MaxMax-embedded/jkbms_hardware_reverse_engineering/images/jk_backside.jpg

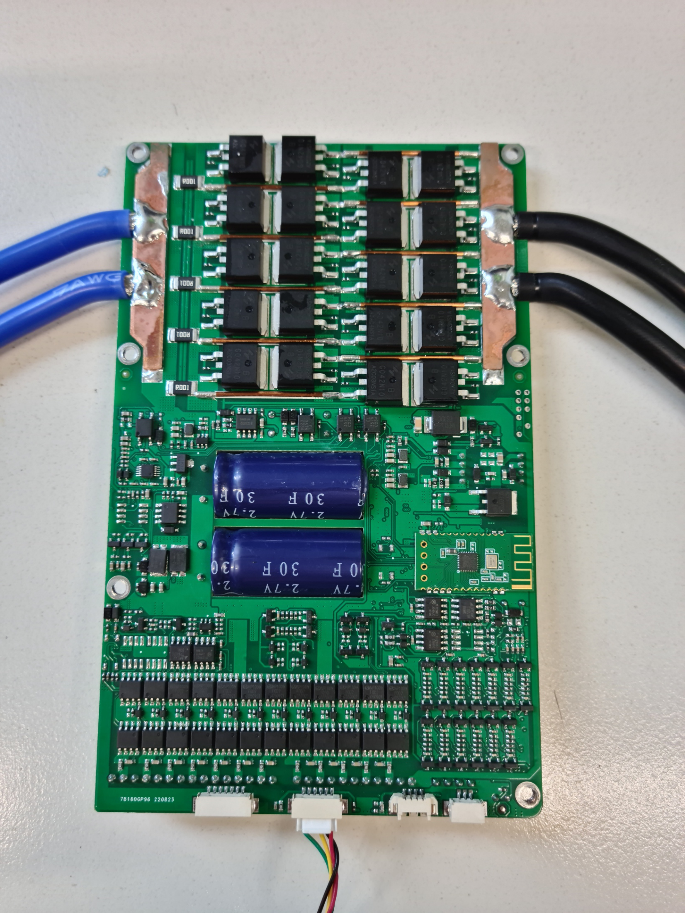
images/jk_backside.jpg
