MaxMax-embedded/jkbms_hardware_reverse_engineering/circuits/balancing_circuitry/balancing_circuitry.kicad_pcb

## KiCad design schematics/Microbee_Kit_Core_Board/Microbee_Kit_Core_Board.kicad_sch

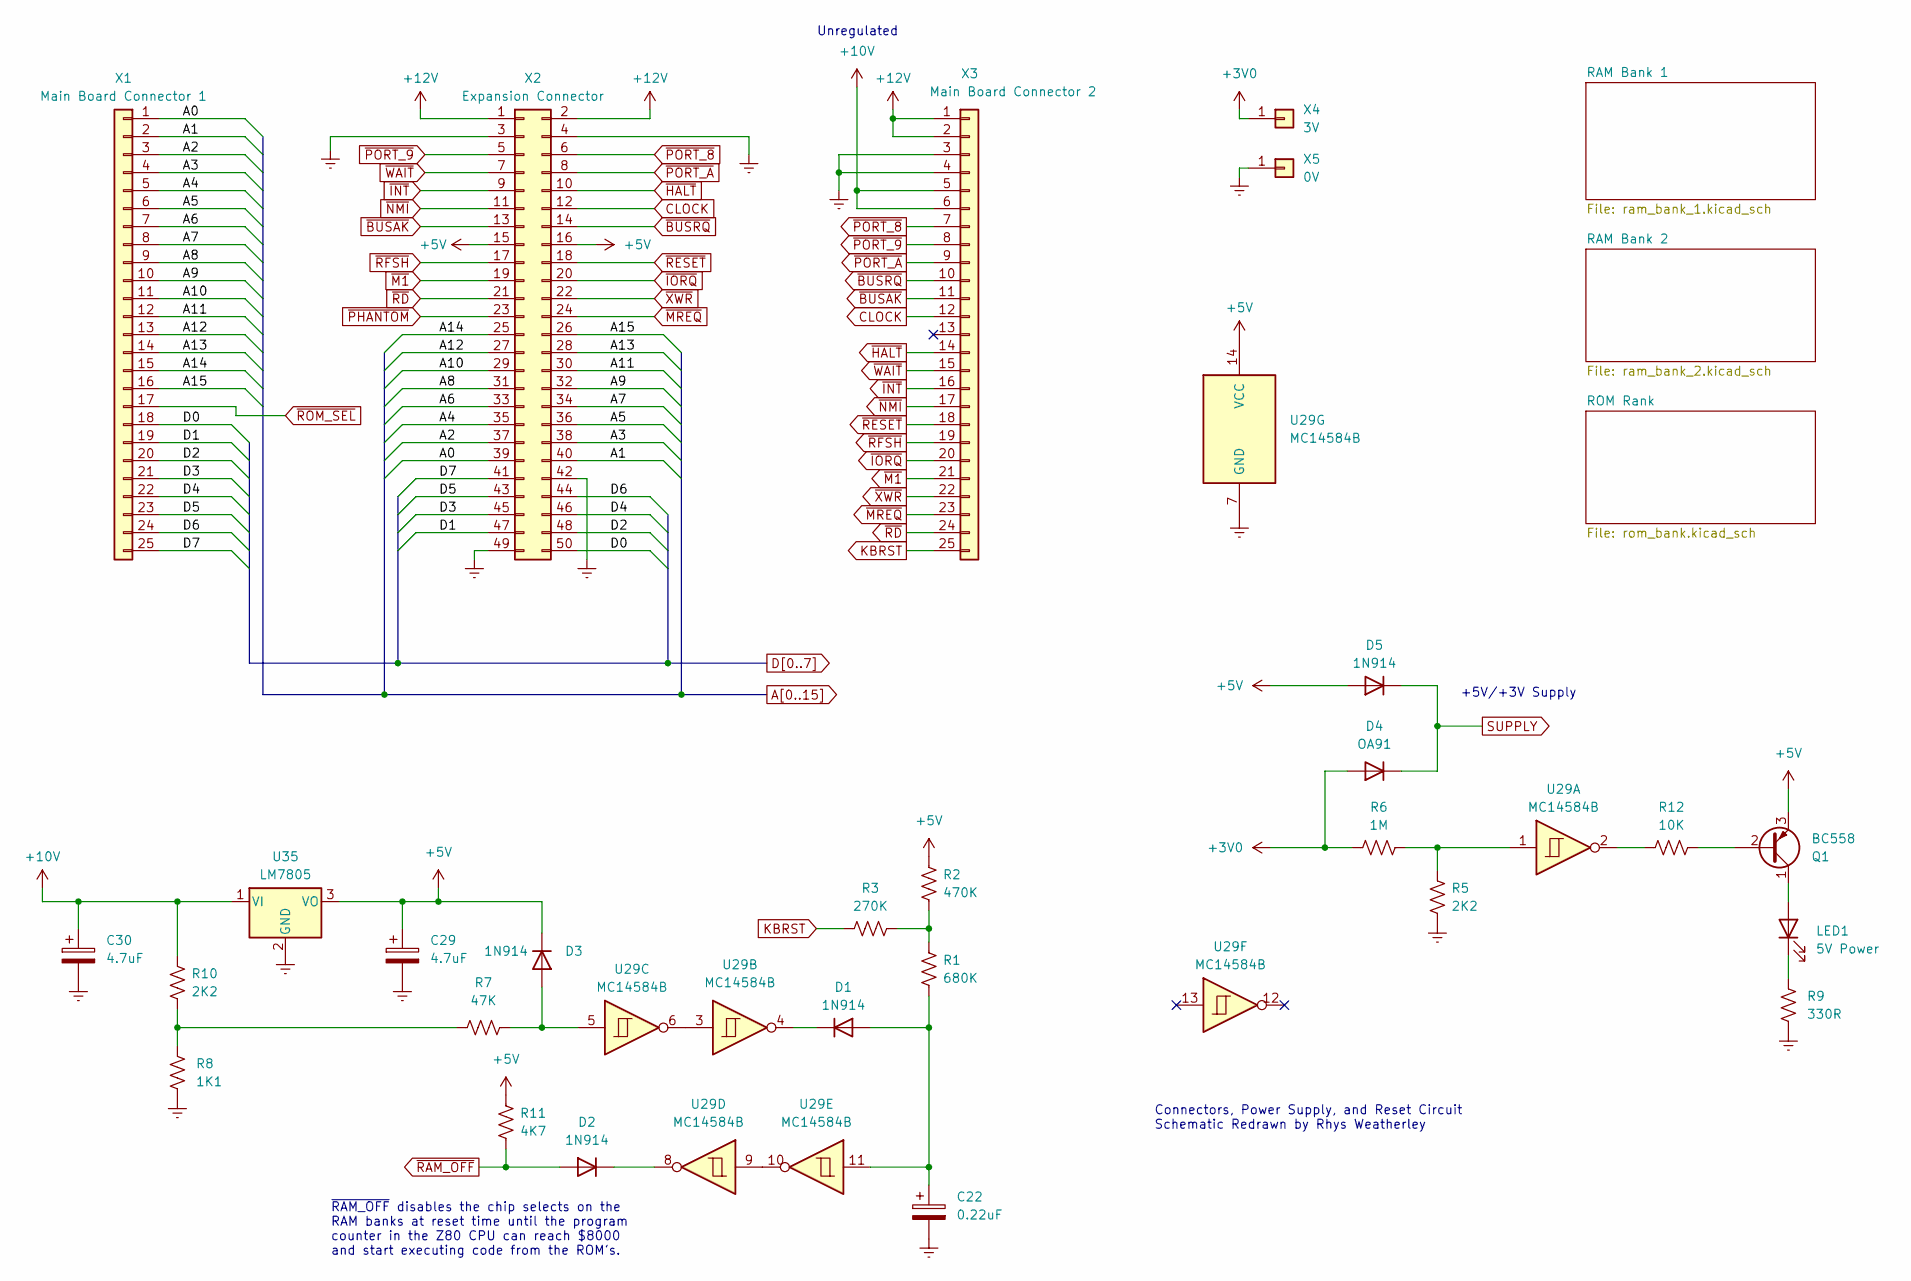
[picture p6: schematic Microbee_Kit_Core_Board.kicad_sch]

Parts:
C22: 0.22uF
C29, C30: 4.7uF
D1, D2, D3, D5: 1N914; D_DO-35_SOD27_P10.16mm_Horizontal
D4: OA91; D_DO-35_SOD27_P10.16mm_Horizontal
LED1: 5V Power
Q1: BC558; TO-92_Inline
R1: 680K; R_Axial_DIN0207_L6.3mm_D2.5mm_P10.16mm_Horizontal
R2: 470K; R_Axial_DIN0207_L6.3mm_D2.5mm_P10.16mm_Horizontal
R3: 270K; R_Axial_DIN0207_L6.3mm_D2.5mm_P10.16mm_Horizontal
R5, R10: 2K2; R_Axial_DIN0207_L6.3mm_D2.5mm_P10.16mm_Horizontal
R6: 1M; R_Axial_DIN0207_L6.3mm_D2.5mm_P10.16mm_Horizontal
R7: 47K; R_Axial_DIN0207_L6.3mm_D2.5mm_P10.16mm_Horizontal
R8: 1K1; R_Axial_DIN0207_L6.3mm_D2.5mm_P10.16mm_Horizontal
R9: 330R; R_Axial_DIN0207_L6.3mm_D2.5mm_P10.16mm_Horizontal
R11: 4K7; R_Axial_DIN0207_L6.3mm_D2.5mm_P10.16mm_Horizontal
R12: 10K; R_Axial_DIN0207_L6.3mm_D2.5mm_P10.16mm_Horizontal
U29: MC14584B; DIP-14_W7.62mm
U35: LM7805; TO-220-3_Vertical
X1: Main Board Connector 1; PinHeader_1x25_P2.54mm_Vertical
X2: Expansion Connector; PinHeader_2x25_P2.54mm_Vertical
X3: Main Board Connector 2; PinHeader_1x25_P2.54mm_Vertical
X4: 3V; PinHeader_1x01_P2.54mm_Vertical
X5: 0V; PinHeader_1x01_P2.54mm_Vertical

Connections:
+3V0: D4.2 (A), R6.1, X4.1
+5V: C29.1, D3.1 (K), D5.2 (A), Q1.3 (E), R2.1, R11.1, U29.14 (VCC), U35.3 (VO), X2.15, X2.16
+10V: C30.1, R10.1, U35.1 (VI), X3.5, X3.6
+12V: X2.1, X2.2, X3.1, X3.2
A0: X1.1, X2.39
A1: X1.2, X2.40
A2: X1.3, X2.37
A3: X1.4, X2.38
A4: X1.5, X2.35
A5: X1.6, X2.36
A6: X1.7, X2.33
A7: X1.8, X2.34
A8: X1.9, X2.31
A9: X1.10, X2.32
A10: X1.11, X2.29
A11: X1.12, X2.30
A12: X1.13, X2.27
A13: X1.14, X2.28
A14: X1.15, X2.25
A15: X1.16, X2.26
CLOCK: X2.12, X3.12
D0: X1.18, X2.50
D1: X1.19, X2.47
D2: X1.20, X2.48
D3: X1.21, X2.45
D4: X1.22, X2.46
D5: X1.23, X2.43
D6: X1.24, X2.44
D7: X1.25, X2.41
Earth: C22.2, C29.2, C30.2, R5.2, R8.2, R9.2, U29.7 (GND), U35.2 (GND), X2.3, X2.4, X2.42, X2.49, X3.3, X3.4, X5.1
KBRST: R3.1, X3.25
unnamed: C22.1, D1.2 (A), R1.2, U29.11
unnamed: D1.1 (K), U29.4
unnamed: D2.1 (K), U29.8
unnamed: D3.2 (A), R7.2, U29.5
unnamed: LED1.1 (K), R9.1
unnamed: LED1.2 (A), Q1.1 (C)
unnamed: Q1.2 (B), R12.2
unnamed: R1.1, R2.2, R3.2
unnamed: R5.1, R6.2, U29.1
unnamed: R7.1, R8.1, R10.2
unnamed: R12.1, U29.2
unnamed: U29.3, U29.6
unnamed: U29.9, U29.10
SUPPLY: D4.1 (K), D5.1 (K)
~BUSAK: X2.13, X3.11
~BUSRQ: X2.14, X3.10
~HALT: X2.10, X3.14
~INT: X2.9, X3.16
~IORQ: X2.20, X3.20
~M1: X2.19, X3.21
~MREQ: X2.24, X3.23
~NMI: X2.11, X3.17
~PHANTOM: X2.23
~PORT_8: X2.6, X3.7
~PORT_9: X2.5, X3.8
~PORT_A: X2.8, X3.9
~RAM_OFF: D2.2 (A), R11.2
~RD: X2.21, X3.24
~RESET: X2.18, X3.18
~RFSH: X2.17, X3.19
~ROM_SEL: X1.17
~WAIT: X2.7, X3.15
~XWR: X2.22, X3.22

Notes on the sheet:
Connectors, Power Supply, and Reset Circuit Schematic Redrawn by Rhys Weatherley
Unregulated
~{RAM_OFF} disables the chip selects on the RAM banks at reset time until the program counter in the Z80 CPU can reach $8000 and start executing code from the ROM's.
+5V/+3V Supply
