MaxMax-embedded/jkbms_hardware_reverse_engineering/circuits/balancing_circuitry/balancing_circuitry.kicad_pcb

## KiCad design schematics/Microbee_Kit_Main_Board/Microbee_Kit_Main_Board.kicad_sch

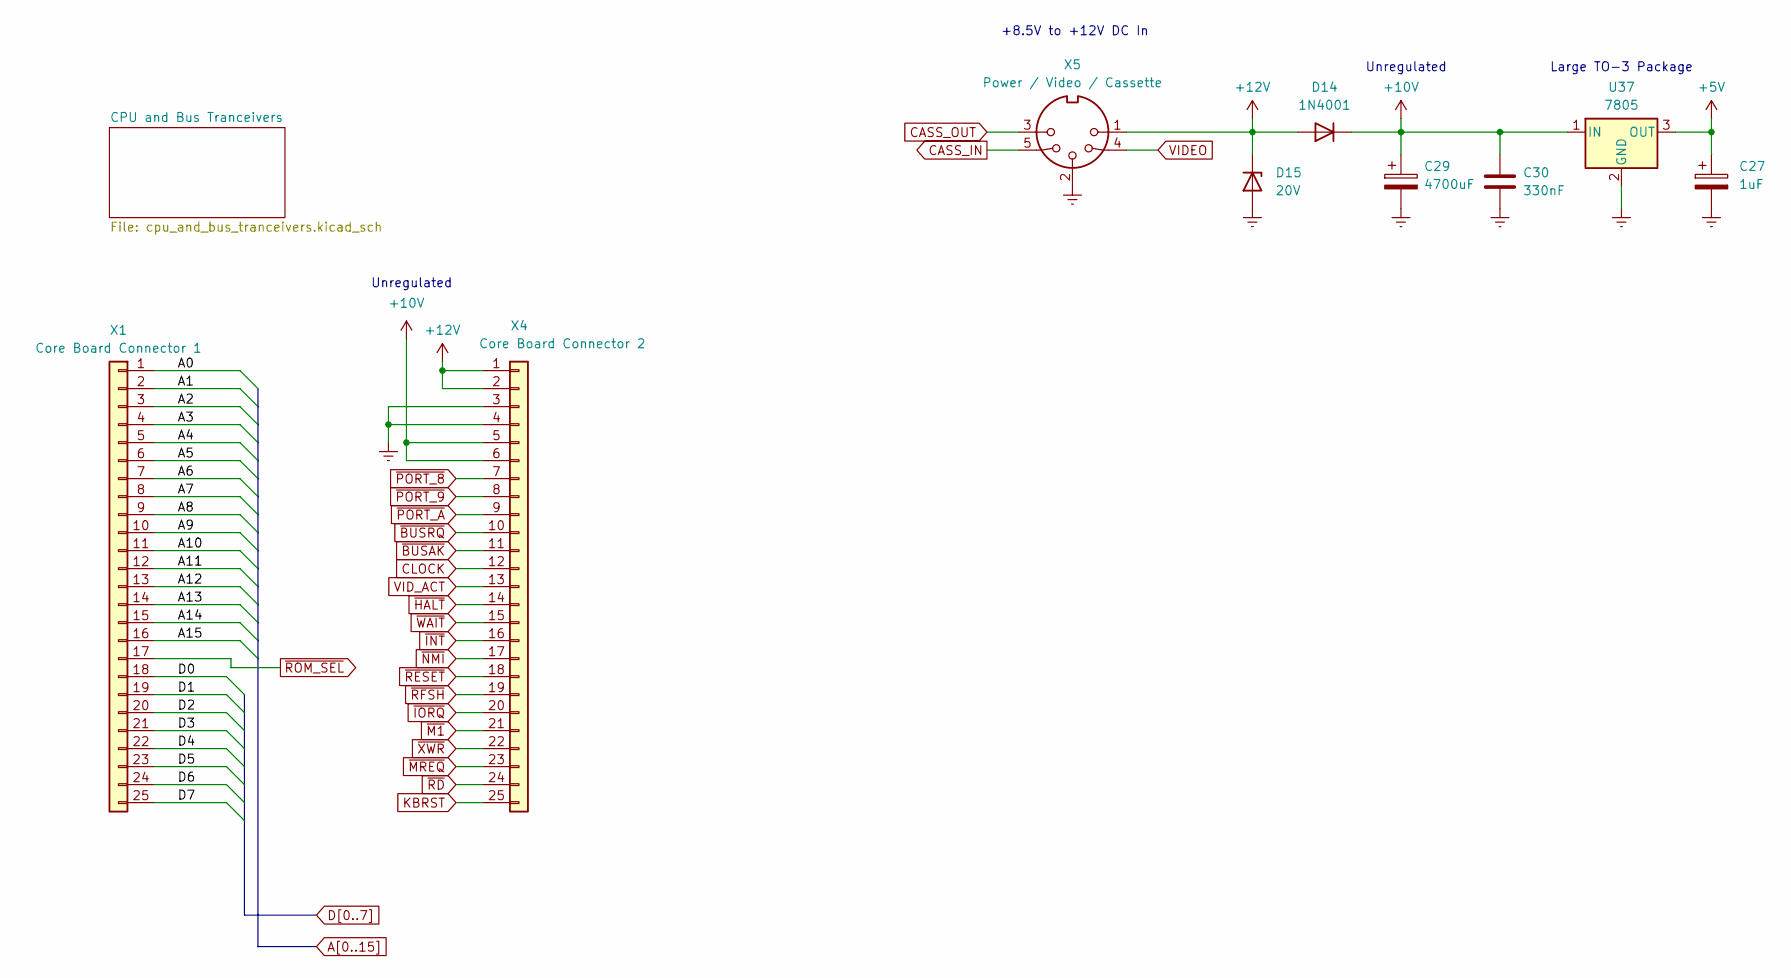
[picture p10: schematic Microbee_Kit_Main_Board.kicad_sch]

Parts:
C27: 1uF
C29: 4700uF
C30: 330nF
D14: 1N4001; D_DO-41_SOD81_P10.16mm_Horizontal
D15: 20V
U37: 7805; TO-3
X1: Core Board Connector 1; PinHeader_1x25_P2.54mm_Vertical
X4: Core Board Connector 2; PinHeader_1x25_P2.54mm_Vertical
X5: Power / Video / Cassette

Connections:
+5V: C27.1, U37.3 (OUT)
+10V: C29.1, C30.1, D14.1 (K), U37.1 (IN), X4.5, X4.6
+12V: D14.2 (A), D15.1 (K), X4.1, X4.2, X5.1
A0: X1.1
A1: X1.2
A2: X1.3
A3: X1.4
A4: X1.5
A5: X1.6
A6: X1.7
A7: X1.8
A8: X1.9
A9: X1.10
A10: X1.11
A11: X1.12
A12: X1.13
A13: X1.14
A14: X1.15
A15: X1.16
CASS_IN: X5.5
CASS_OUT: X5.3
CLOCK: X4.12
D0: X1.18
D1: X1.19
D2: X1.20
D3: X1.21
D4: X1.22
D5: X1.23
D6: X1.24
D7: X1.25
Earth: C27.2, C29.2, C30.2, D15.2 (A), U37.2 (GND), X4.3, X4.4, X5.2
KBRST: X4.25
VIDEO: X5.4
VID_ACT: X4.13
~BUSAK: X4.11
~BUSRQ: X4.10
~HALT: X4.14
~INT: X4.16
~IORQ: X4.20
~M1: X4.21
~MREQ: X4.23
~NMI: X4.17
~PORT_8: X4.7
~PORT_9: X4.8
~PORT_A: X4.9
~RD: X4.24
~RESET: X4.18
~RFSH: X4.19
~ROM_SEL: X1.17
~WAIT: X4.15
~XWR: X4.22

Notes on the sheet:
Large TO-3 Package
Unregulated
+8.5V to +12V DC In
