MaxMax-embedded/jkbms_hardware_reverse_engineering/circuits/balancing_circuitry/balancing_circuitry.kicad_pcb

## KiCad design schematics/Microbee_Kit_Main_Board/character_generation.kicad_sch

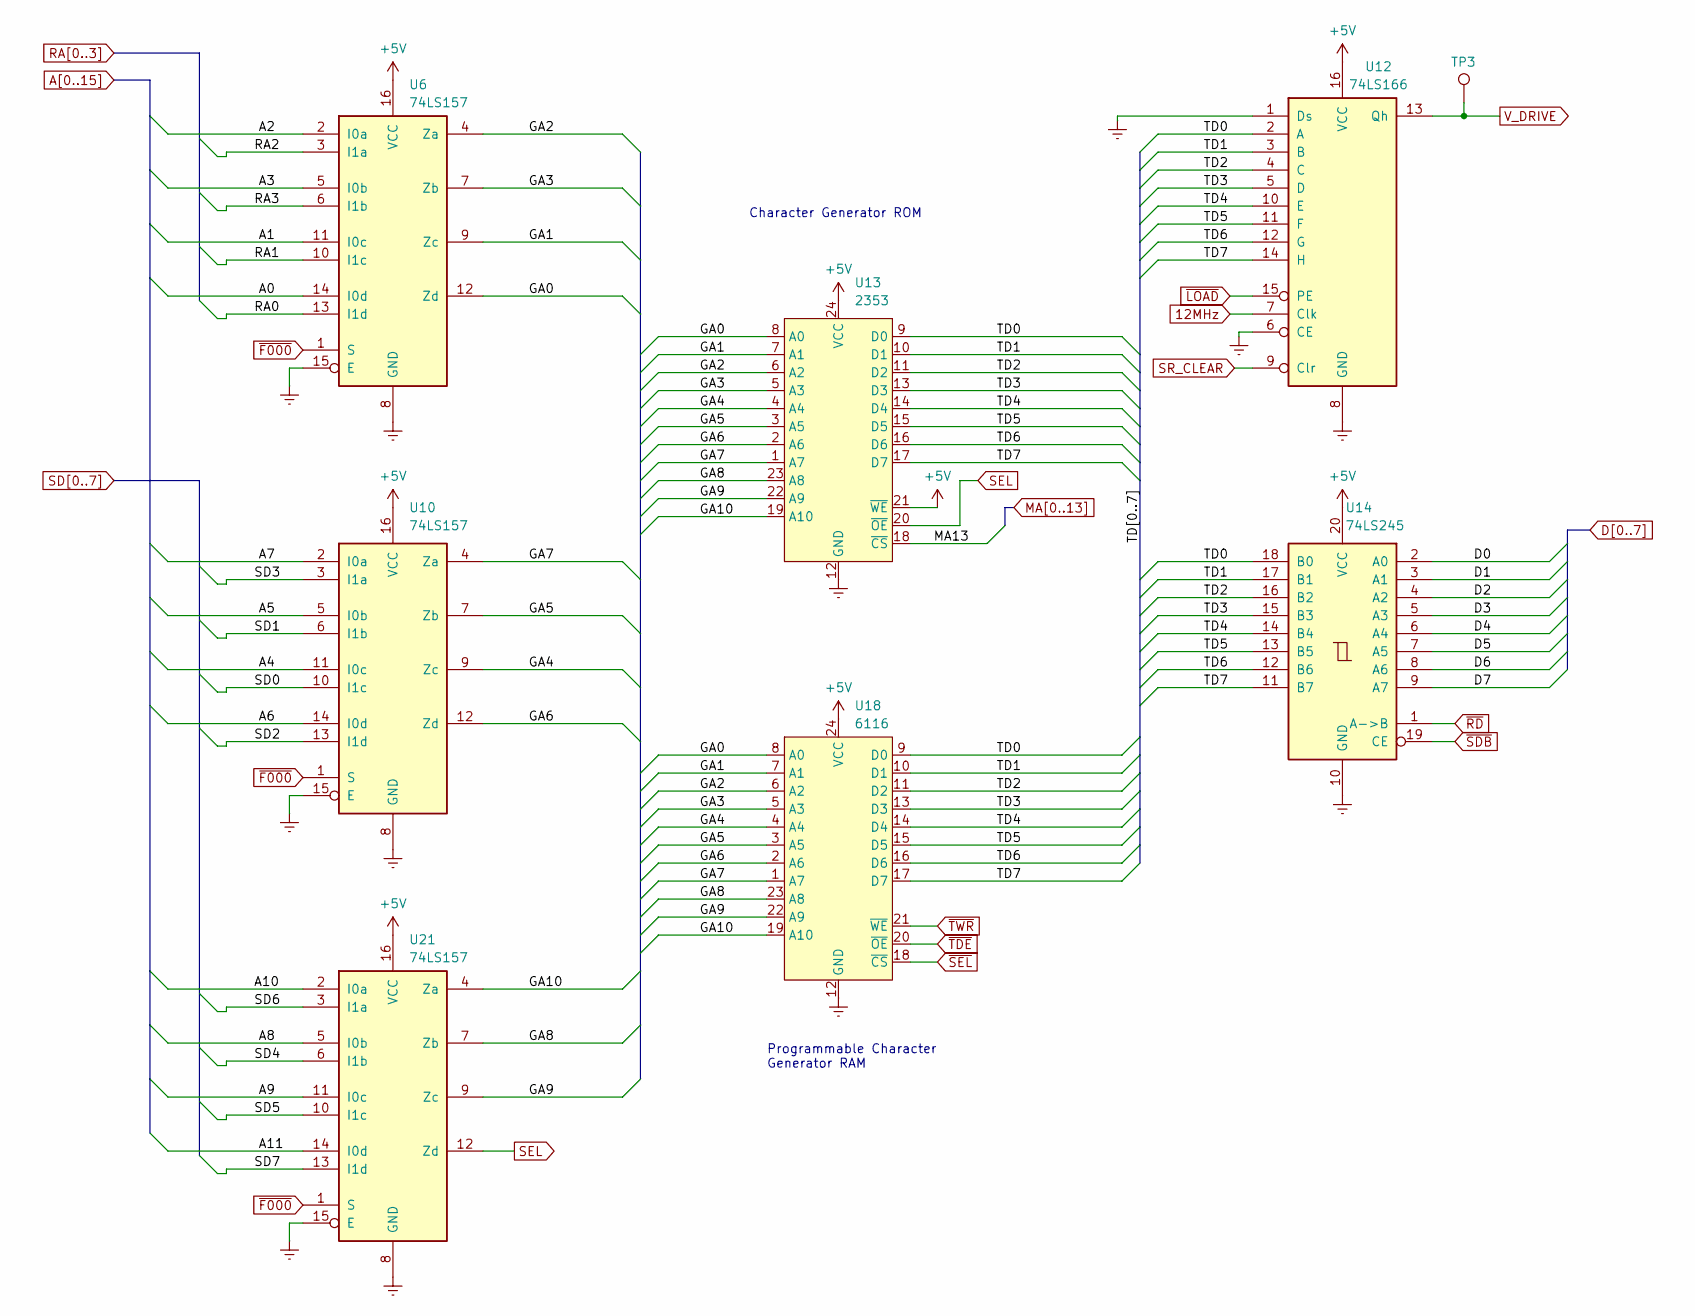
[picture p11: schematic character_generation.kicad_sch]

Parts:
TP3: TestPoint
U6, U10, U21: 74LS157; DIP-16_W7.62mm
U12: 74LS166; DIP-16_W7.62mm
U13: 2353; DIP-24_W15.24mm
U14: 74LS245; DIP-20_W7.62mm
U18: 6116; DIP-24_W15.24mm

Connections:
12MHz: U12.7 (Clk)
+5V: U6.16 (VCC), U10.16 (VCC), U12.16 (VCC), U13.21 (~WE), U13.24 (VCC), U14.20 (VCC), U18.24 (VCC), U21.16 (VCC)
A0: U6.14 (I0d)
A1: U6.11 (I0c)
A2: U6.2 (I0a)
A3: U6.5 (I0b)
A4: U10.11 (I0c)
A5: U10.5 (I0b)
A6: U10.14 (I0d)
A7: U10.2 (I0a)
A8: U21.5 (I0b)
A9: U21.11 (I0c)
A10: U21.2 (I0a)
A11: U21.14 (I0d)
D0: U14.2 (A0)
D1: U14.3 (A1)
D2: U14.4 (A2)
D3: U14.5 (A3)
D4: U14.6 (A4)
D5: U14.7 (A5)
D6: U14.8 (A6)
D7: U14.9 (A7)
Earth: U6.8 (GND), U6.15 (E), U10.8 (GND), U10.15 (E), U12.1 (Ds), U12.6 (CE), U12.8 (GND), U13.12 (GND), U14.10 (GND), U18.12 (GND), U21.8 (GND), U21.15 (E)
GA0: U6.12 (Zd), U13.8 (A0), U18.8 (A0)
GA1: U6.9 (Zc), U13.7 (A1), U18.7 (A1)
GA2: U6.4 (Za), U13.6 (A2), U18.6 (A2)
GA3: U6.7 (Zb), U13.5 (A3), U18.5 (A3)
GA4: U10.9 (Zc), U13.4 (A4), U18.4 (A4)
GA5: U10.7 (Zb), U13.3 (A5), U18.3 (A5)
GA6: U10.12 (Zd), U13.2 (A6), U18.2 (A6)
GA7: U10.4 (Za), U13.1 (A7), U18.1 (A7)
GA8: U13.23 (A8), U18.23 (A8), U21.7 (Zb)
GA9: U13.22 (A9), U18.22 (A9), U21.9 (Zc)
GA10: U13.19 (A10), U18.19 (A10), U21.4 (Za)
MA13: U13.18 (~CS)
RA0: U6.13 (I1d)
RA1: U6.10 (I1c)
RA2: U6.3 (I1a)
RA3: U6.6 (I1b)
SD0: U10.10 (I1c)
SD1: U10.6 (I1b)
SD2: U10.13 (I1d)
SD3: U10.3 (I1a)
SD4: U21.6 (I1b)
SD5: U21.10 (I1c)
SD6: U21.3 (I1a)
SD7: U21.13 (I1d)
SEL: U13.20 (~OE), U21.12 (Zd)
SR_CLEAR: U12.9 (Clr)
TD0: U12.2 (A), U13.9 (D0), U14.18 (B0), U18.9 (D0)
TD1: U12.3 (B), U13.10 (D1), U14.17 (B1), U18.10 (D1)
TD2: U12.4 (C), U13.11 (D2), U14.16 (B2), U18.11 (D2)
TD3: U12.5 (D), U13.13 (D3), U14.15 (B3), U18.13 (D3)
TD4: U12.10 (E), U13.14 (D4), U14.14 (B4), U18.14 (D4)
TD5: U12.11 (F), U13.15 (D5), U14.13 (B5), U18.15 (D5)
TD6: U12.12 (G), U13.16 (D6), U14.12 (B6), U18.16 (D6)
TD7: U12.14 (H), U13.17 (D7), U14.11 (B7), U18.17 (D7)
V_DRIVE: TP3.1, U12.13 (Qh)
~F000: U6.1 (S), U10.1 (S), U21.1 (S)
~LOAD: U12.15 (PE)
~RD: U14.1 (A->B)
~SDB: U14.19 (CE)
~SEL: U18.18 (~CS)
~TDE: U18.20 (~OE)
~TWR: U18.21 (~WE)

Notes on the sheet:
Character Generator ROM
Programmable Character Generator RAM
