MaxMax-embedded/jkbms_hardware_reverse_engineering/circuits/balancing_circuitry/balancing_circuitry.kicad_pcb

## KiCad design schematics/Microbee_Kit_Main_Board/keyboard.kicad_sch

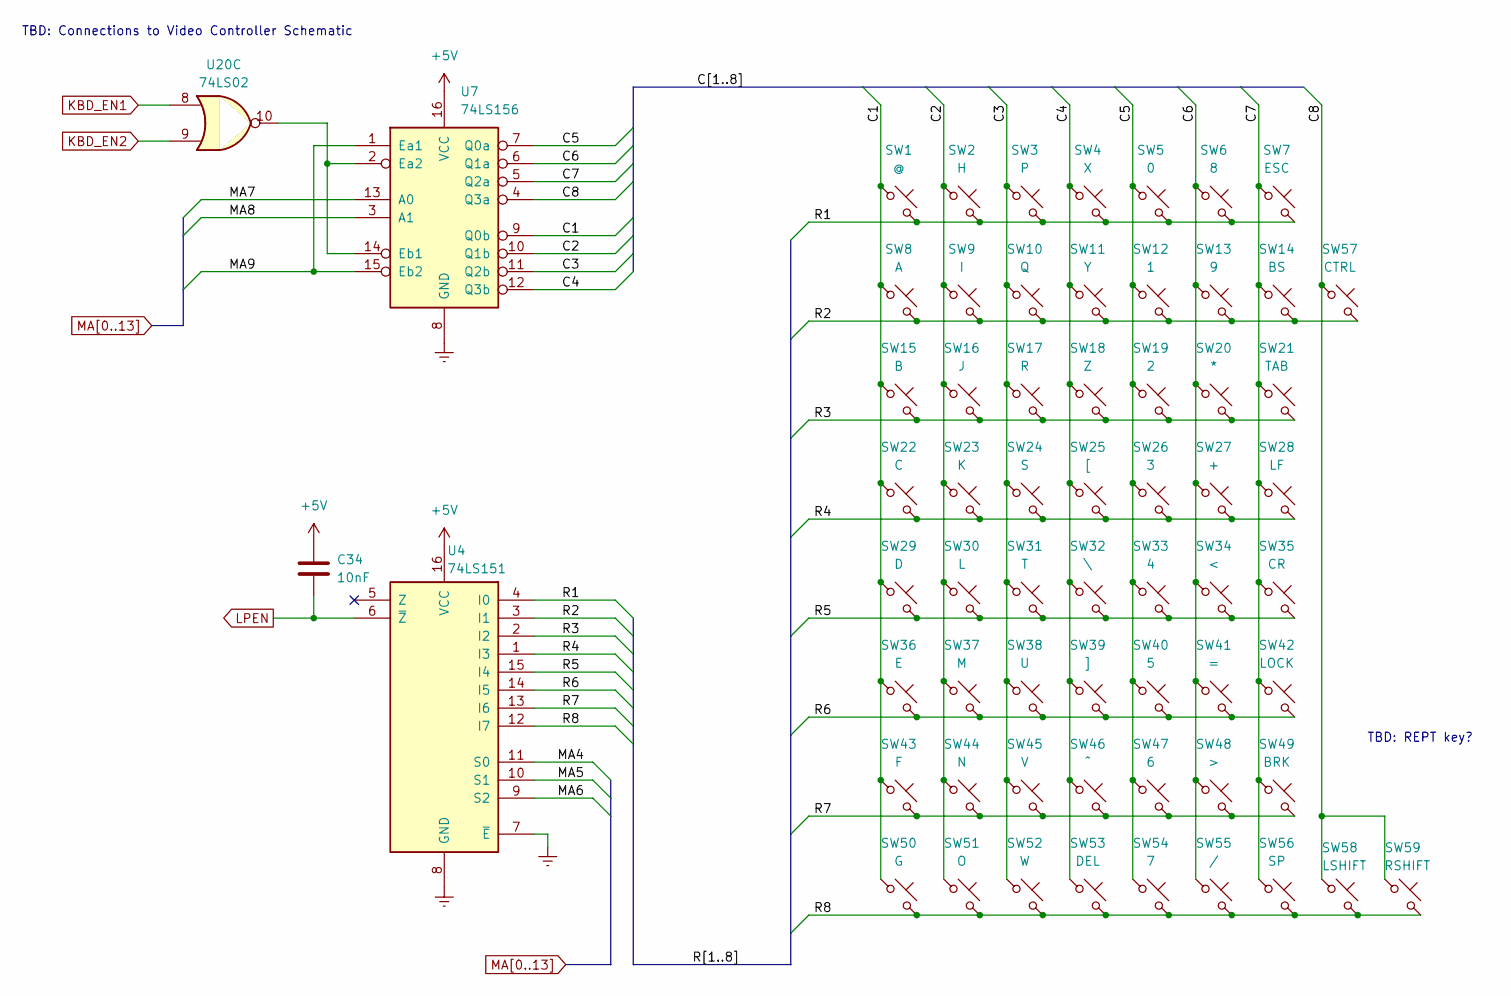
[picture p15: schematic keyboard.kicad_sch]

Parts:
C34: 10nF
SW1: @
SW2: H
SW3: P
SW4: X
SW5: 0
SW6: 8
SW7: ESC
SW8: A
SW9: I
SW10: Q
SW11: Y
SW12: 1
SW13: 9
SW14: BS
SW15: B
SW16: J
SW17: R
SW18: Z
SW19: 2
SW20: *
SW21: TAB
SW22: C
SW23: K
SW24: S
SW25: [
SW26: 3
SW27: +
SW28: LF
SW29: D
SW30: L
SW31: T
SW32: \
SW33: 4
SW34: <
SW35: CR
SW36: E
SW37: M
SW38: U
SW39: ]
SW40: 5
SW41: =
SW42: LOCK
SW43: F
SW44: N
SW45: V
SW46: ^
SW47: 6
SW48: >
SW49: BRK
SW50: G
SW51: O
SW52: W
SW53: DEL
SW54: 7
SW55: /
SW56: SP
SW57: CTRL
SW58: LSHIFT
SW59: RSHIFT
U4: 74LS151; DIP-16_W7.62mm
U7: 74LS156; DIP-16_W7.62mm
U20: 74LS02

Connections:
+5V: C34.1, U4.16 (VCC), U7.16 (VCC)
C1: SW1.1, SW8.1, SW15.1, SW22.1, SW29.1, SW36.1, SW43.1, SW50.1, U7.9 (Q0b)
C2: SW2.1, SW9.1, SW16.1, SW23.1, SW30.1, SW37.1, SW44.1, SW51.1, U7.10 (Q1b)
C3: SW3.1, SW10.1, SW17.1, SW24.1, SW31.1, SW38.1, SW45.1, SW52.1, U7.11 (Q2b)
C4: SW4.1, SW11.1, SW18.1, SW25.1, SW32.1, SW39.1, SW46.1, SW53.1, U7.12 (Q3b)
C5: SW5.1, SW12.1, SW19.1, SW26.1, SW33.1, SW40.1, SW47.1, SW54.1, U7.7 (Q0a)
C6: SW6.1, SW13.1, SW20.1, SW27.1, SW34.1, SW41.1, SW48.1, SW55.1, U7.6 (Q1a)
C7: SW7.1, SW14.1, SW21.1, SW28.1, SW35.1, SW42.1, SW49.1, SW56.1, U7.5 (Q2a)
C8: SW57.1, SW58.1, SW59.1, U7.4 (Q3a)
Earth: U4.7 (~E), U4.8 (GND), U7.8 (GND)
KBD_EN1: U20.8
KBD_EN2: U20.9
LPEN: C34.2, U4.6 (~Z)
MA4: U4.11 (S0)
MA5: U4.10 (S1)
MA6: U4.9 (S2)
MA7: U7.13 (A0)
MA8: U7.3 (A1)
MA9: U7.1 (Ea1), U7.15 (Eb2)
unnamed: U7.2 (Ea2), U7.14 (Eb1), U20.10
R1: SW1.2, SW2.2, SW3.2, SW4.2, SW5.2, SW6.2, SW7.2, U4.4 (I0)
R2: SW8.2, SW9.2, SW10.2, SW11.2, SW12.2, SW13.2, SW14.2, SW57.2, U4.3 (I1)
R3: SW15.2, SW16.2, SW17.2, SW18.2, SW19.2, SW20.2, SW21.2, U4.2 (I2)
R4: SW22.2, SW23.2, SW24.2, SW25.2, SW26.2, SW27.2, SW28.2, U4.1 (I3)
R5: SW29.2, SW30.2, SW31.2, SW32.2, SW33.2, SW34.2, SW35.2, U4.15 (I4)
R6: SW36.2, SW37.2, SW38.2, SW39.2, SW40.2, SW41.2, SW42.2, U4.14 (I5)
R7: SW43.2, SW44.2, SW45.2, SW46.2, SW47.2, SW48.2, SW49.2, U4.13 (I6)
R8: SW50.2, SW51.2, SW52.2, SW53.2, SW54.2, SW55.2, SW56.2, SW58.2, SW59.2, U4.12 (I7)

Notes on the sheet:
TBD: REPT key?
TBD: Connections to Video Controller Schematic
